mayvid22/Solinas-Product-Design-Challenge/Solinas CAD/Mount/stand assembly/top motor/Component8.step

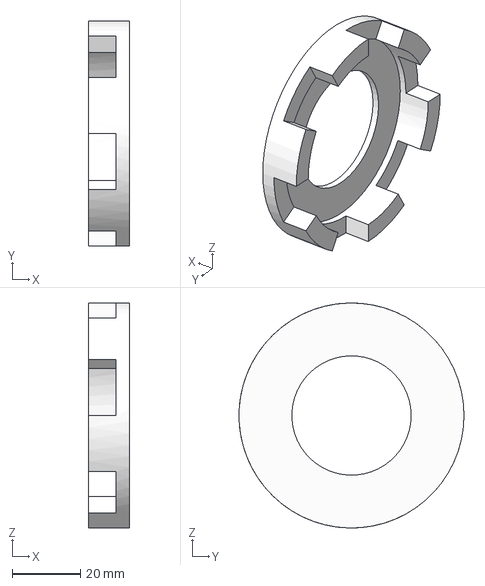
[picture p5: CAD file, 2024-07-06]
Solinas CAD/Mount/stand assembly/top motor/Component8.step
12.0 x 66.0 x 66.0 mm
