mayvid22/Solinas-Product-Design-Challenge/Solinas CAD/Mount/stand support/Part6.step

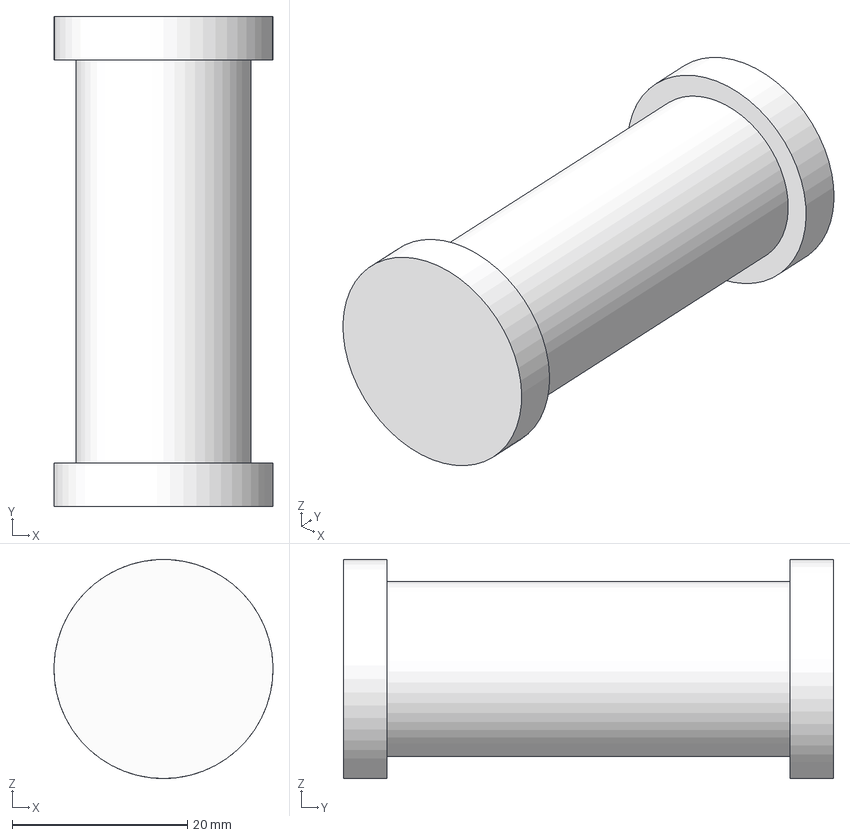
[picture p15: CAD file, 2024-07-06]
Solinas CAD/Mount/stand support/Part6.step
25.0 x 56.0 x 25.0 mm
