mayvid22/Solinas-Product-Design-Challenge/Solinas CAD/Mount/upper part/Component1.step

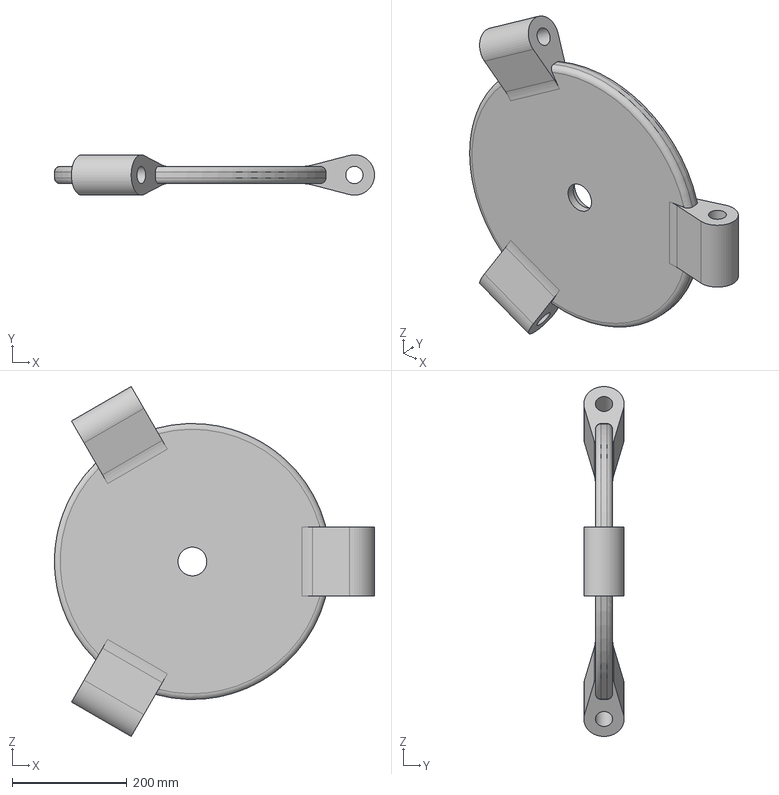
[picture p16: CAD file, 2024-07-06]
Solinas CAD/Mount/upper part/Component1.step
556.9 x 70.3 x 608.9 mm
