mayvid22/Solinas-Product-Design-Challenge/Solinas CAD/Mount/wheel stand/Component3.step

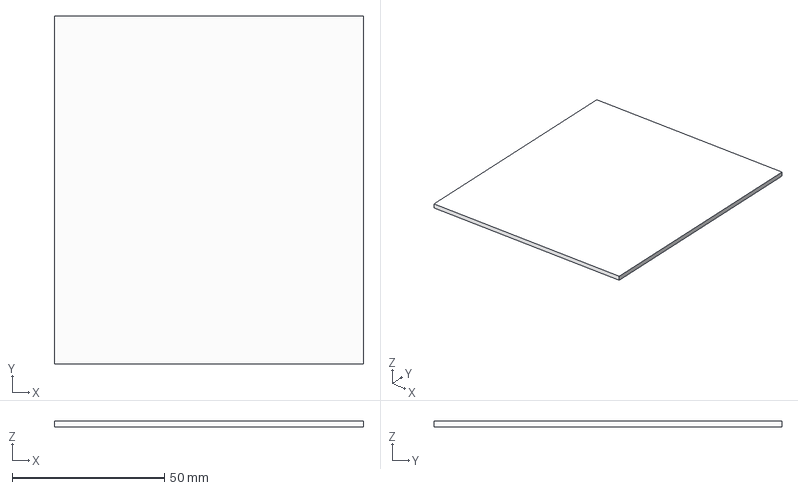
[picture p17: CAD file, 2024-07-06]
Solinas CAD/Mount/wheel stand/Component3.step
101.6 x 114.3 x 2.00 mm
