mayvid22/Solinas-Product-Design-Challenge/Solinas CAD/Shaft/1st cylinder/Component1.step

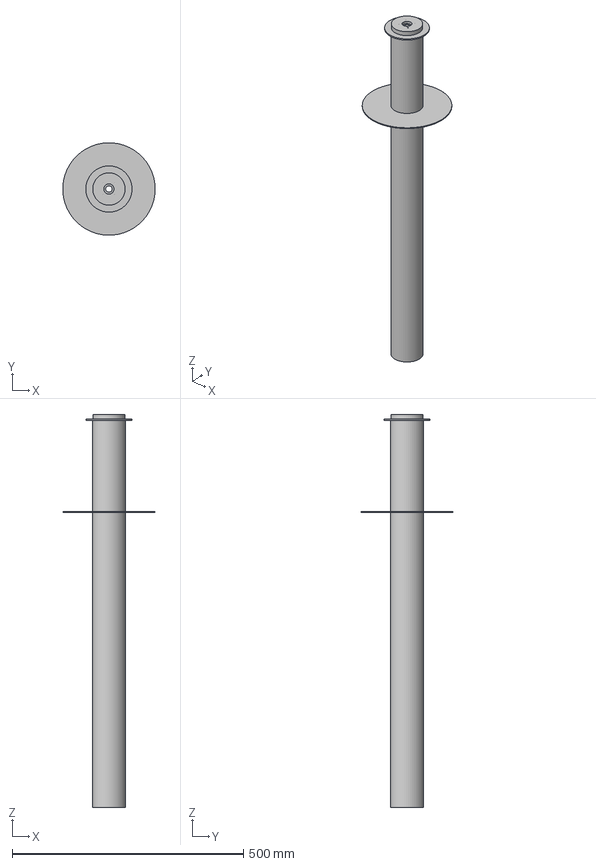
[picture p18: CAD file, 2024-07-06]
Solinas CAD/Shaft/1st cylinder/Component1.step
199.8 x 199.9 x 850.0 mm
