mayvid22/Solinas-Product-Design-Challenge/Solinas CAD/Shaft/1st cylinder/coupler/coupler v1.step

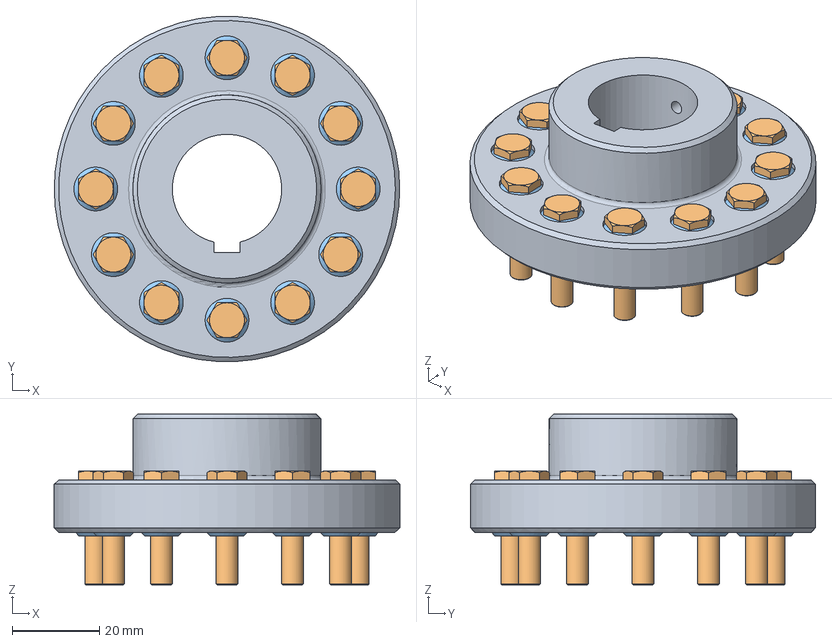
[picture p19: CAD file, 2024-07-06]
Solinas CAD/Shaft/1st cylinder/coupler/coupler v1.step
79.0 x 78.9 x 39.0 mm
c1
csavarr x 12
gumi anya x 48
