mayvid22/Solinas-Product-Design-Challenge/Solinas CAD/Shaft/2nd cylinder/2nd wear ring v4.step

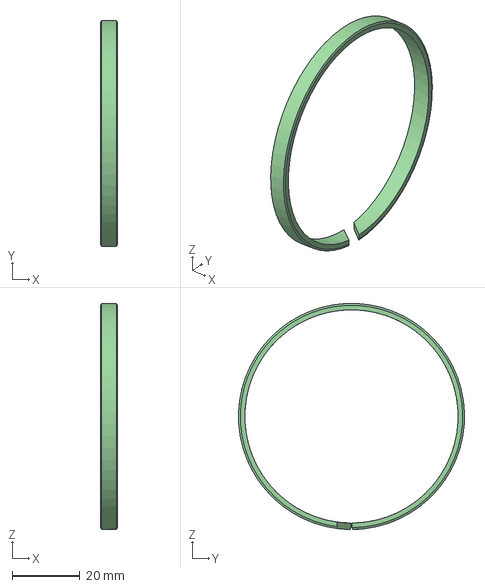
[picture p20: CAD file, 2024-07-06]
Solinas CAD/Shaft/2nd cylinder/2nd wear ring v4.step
5.00 x 67.0 x 67.0 mm
