mayvid22/Solinas-Product-Design-Challenge/Solinas CAD/Shaft/3rd cylinder/3rd wear ring v3.step

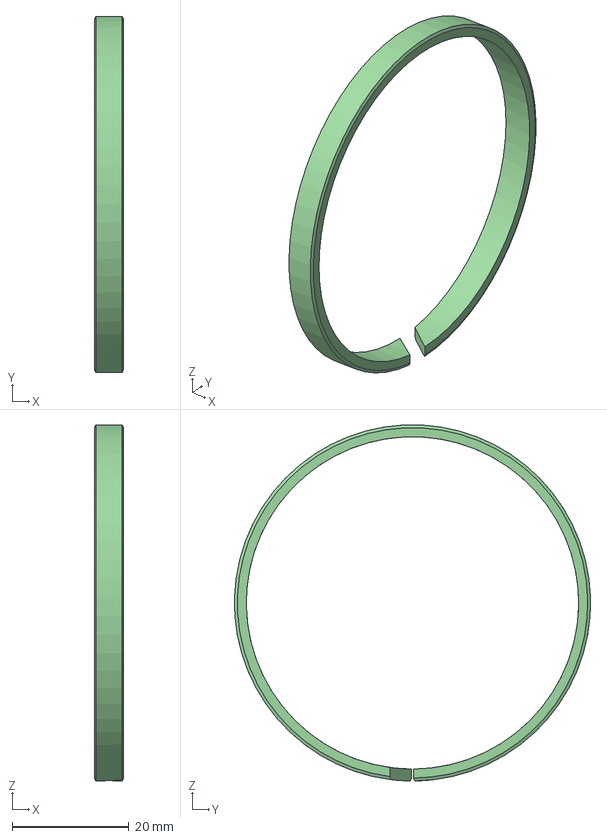
[picture p21: CAD file, 2024-07-06]
Solinas CAD/Shaft/3rd cylinder/3rd wear ring v3.step
5.00 x 61.0 x 61.0 mm
