mayvid22/Solinas-Product-Design-Challenge/Solinas CAD/Shaft/4th cylinder/4th wiper seal v3.step

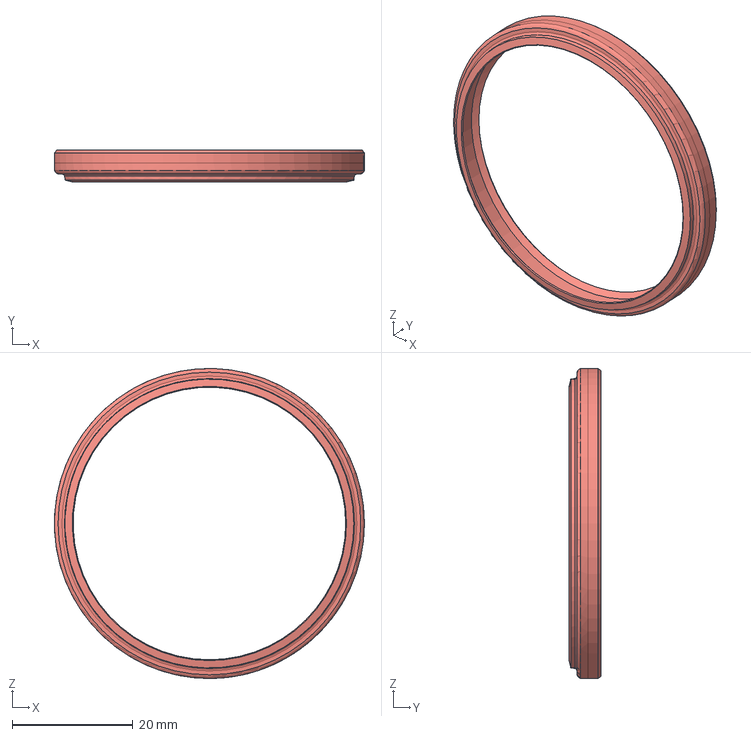
[picture p22: CAD file, 2024-07-06]
Solinas CAD/Shaft/4th cylinder/4th wiper seal v3.step
51.4 x 5.29 x 51.4 mm
