mayvid22/Solinas-Product-Design-Challenge/Solinas CAD/Shaft/5th cylinder/5th wiper seal v2.step

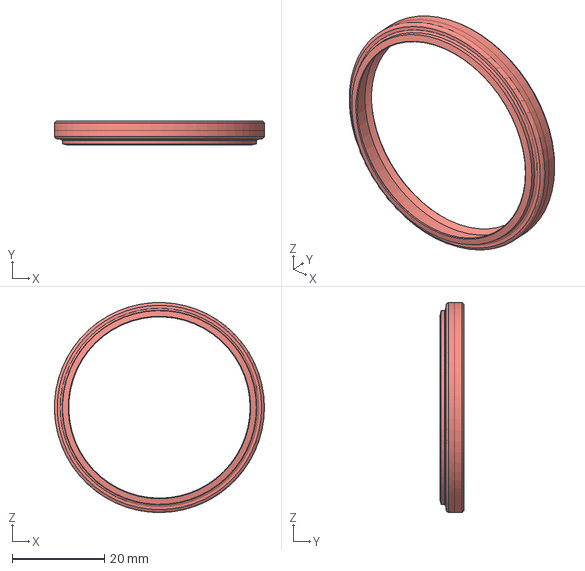
[picture p23: CAD file, 2024-07-06]
Solinas CAD/Shaft/5th cylinder/5th wiper seal v2.step
45.4 x 5.29 x 45.4 mm
