mayvid22/Solinas-Product-Design-Challenge/Solinas CAD/Shaft/6th cylinder/6th wiper seal v4.step

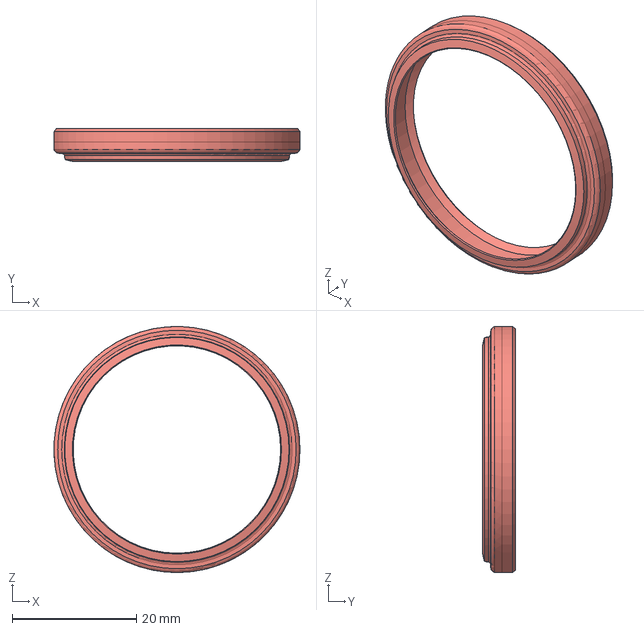
[picture p24: CAD file, 2024-07-06]
Solinas CAD/Shaft/6th cylinder/6th wiper seal v4.step
39.6 x 5.29 x 39.6 mm
