mayvid22/Solinas-Product-Design-Challenge/Solinas CAD/Mount/outer part/Component3.step

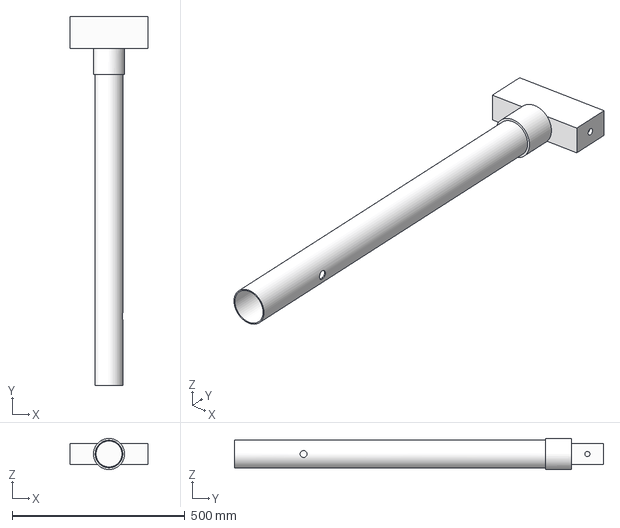
[picture p25: CAD file, 2024-07-06]
Solinas CAD/Mount/outer part/Component3.step
225.0 x 1068.0 x 90.0 mm
