mayvid22/Solinas-Product-Design-Challenge/Solinas CAD/Mount/ratchet_hinge_mirror1.step

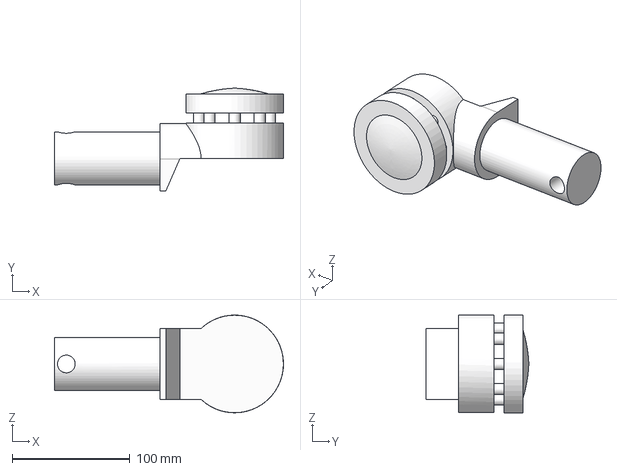
[picture p26: CAD file, 2024-07-06]
Solinas CAD/Mount/ratchet_hinge_mirror1.step
194.4 x 87.2 x 82.9 mm
