mayvid22/Solinas-Product-Design-Challenge/Solinas CAD/Mount/stand assembly/top motor/_MS-SP.step

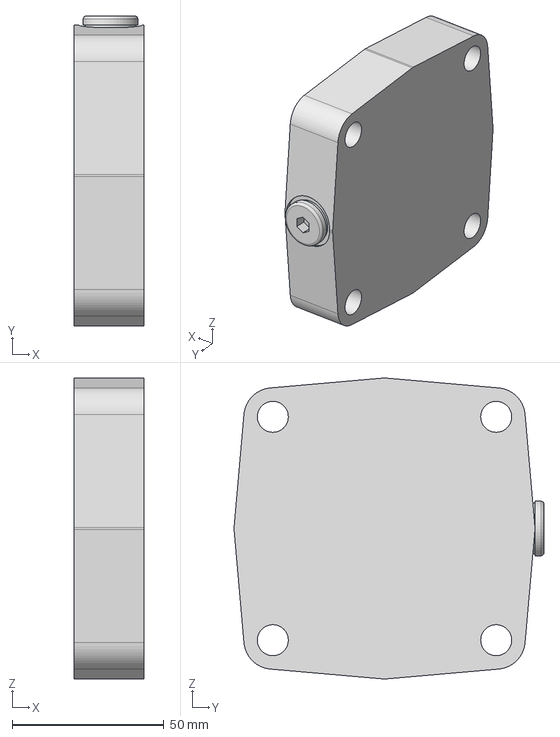
[picture p27: CAD file, 2024-07-06]
Solinas CAD/Mount/stand assembly/top motor/_MS-SP.step
23.0 x 102.0 x 99.1 mm
