mayvid22/Solinas-Product-Design-Challenge/Solinas CAD/Mount/upper part/upper part v7.step

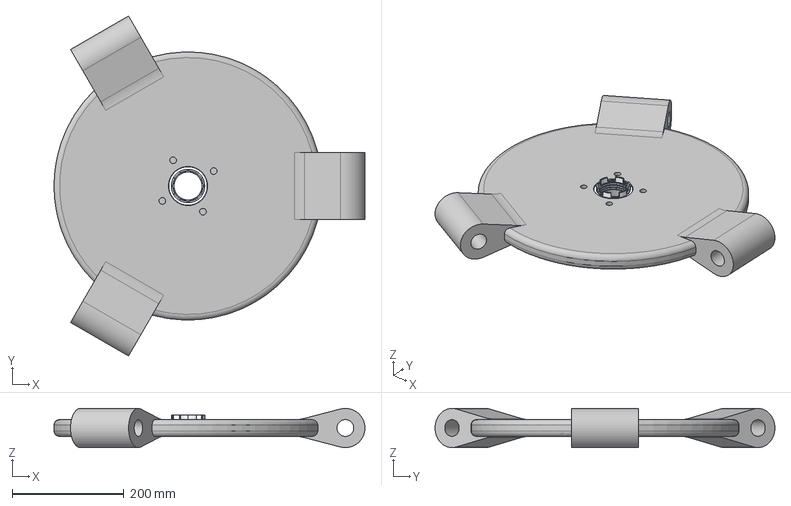
[picture p28: CAD file, 2024-07-06]
Solinas CAD/Mount/upper part/upper part v7.step
556.9 x 608.9 x 70.3 mm
4300N19_Cylindrical-Roller Thrust Bearing
