mayvid22/Solinas-Product-Design-Challenge/Solinas CAD/Mount/wheel stand/castor wheel.step

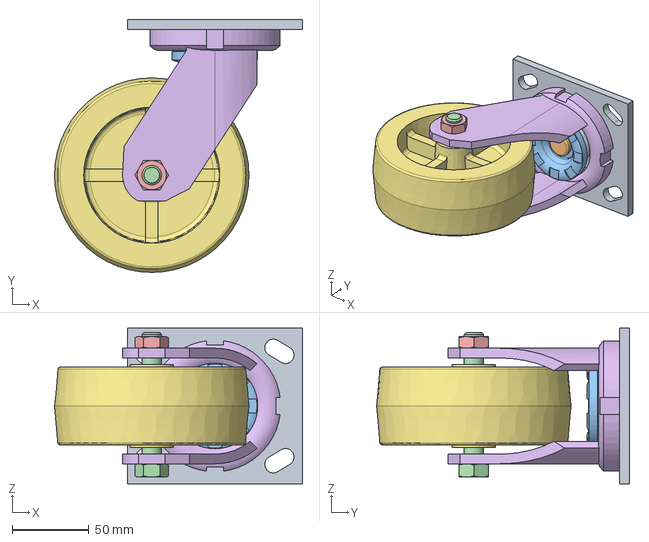
[picture p29: CAD file, 2024-07-06]
Solinas CAD/Mount/wheel stand/castor wheel.step
161.9 x 165.1 x 101.6 mm
