mayvid22/Solinas-Product-Design-Challenge/Solinas CAD/Shaft/1st cylinder/coupler/c1.step

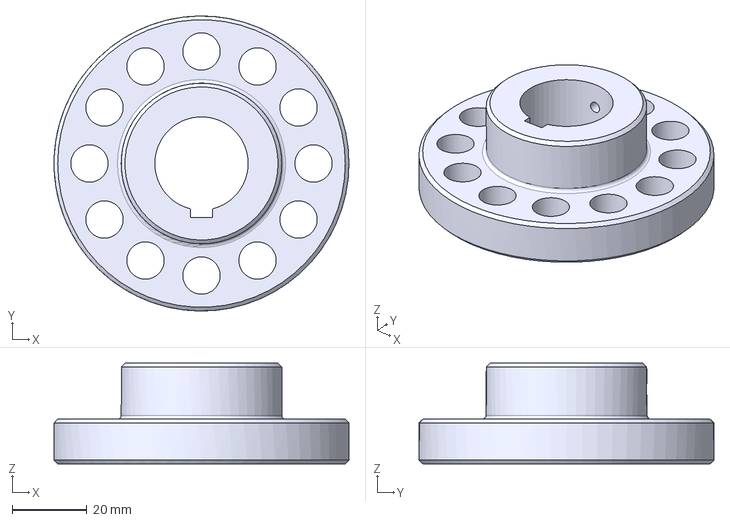
[picture p30: CAD file, 2024-07-06]
Solinas CAD/Shaft/1st cylinder/coupler/c1.step
79.0 x 79.0 x 27.0 mm
