mayvid22/Solinas-Product-Design-Challenge/Solinas CAD/Shaft/2nd cylinder/Component1.step

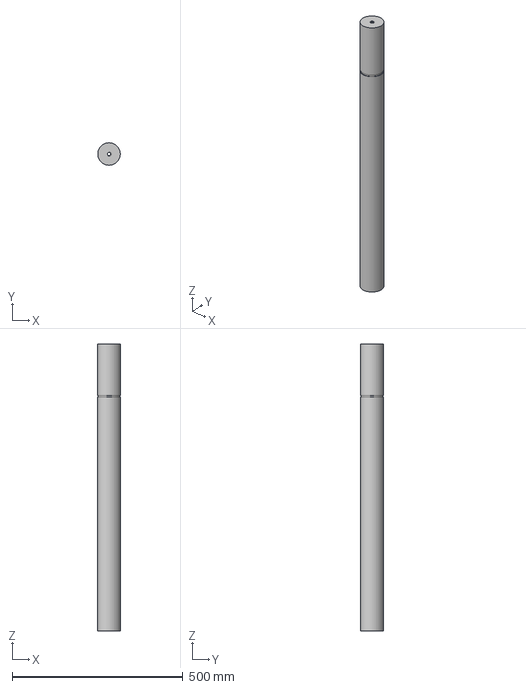
[picture p31: CAD file, 2024-07-06]
Solinas CAD/Shaft/2nd cylinder/Component1.step
65.9 x 66.0 x 840.0 mm
