mayvid22/Solinas-Product-Design-Challenge/Solinas CAD/Shaft/3rd cylinder/Component1.step

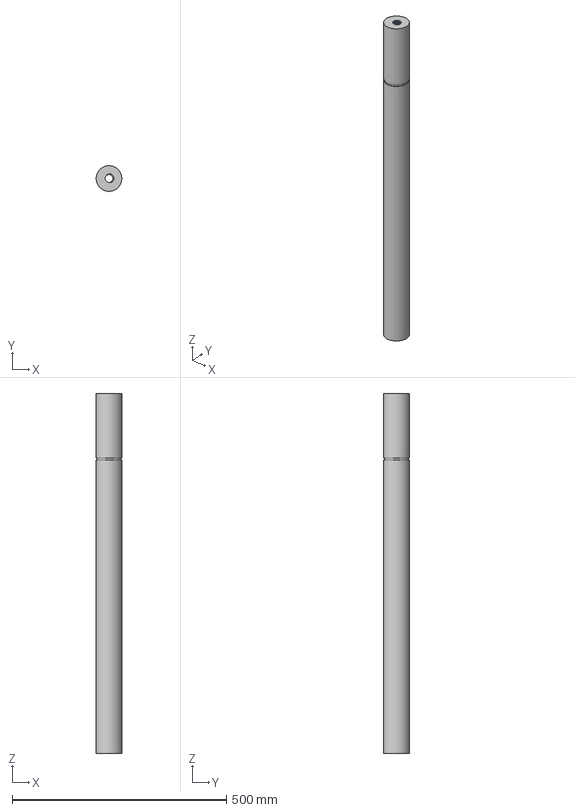
[picture p32: CAD file, 2024-07-06]
Solinas CAD/Shaft/3rd cylinder/Component1.step
59.9 x 60.0 x 840.0 mm
