mayvid22/Solinas-Product-Design-Challenge/Solinas CAD/Shaft/4th cylinder/4th wear ring v4.step

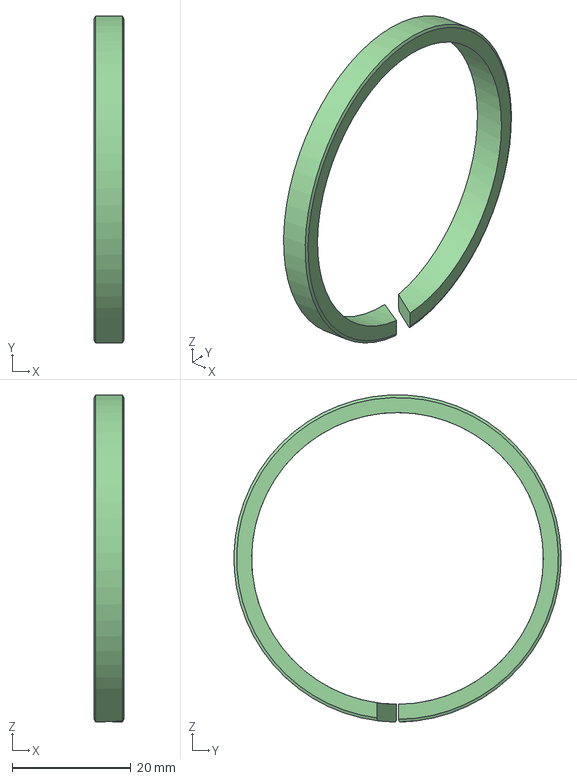
[picture p33: CAD file, 2024-07-06]
Solinas CAD/Shaft/4th cylinder/4th wear ring v4.step
5.00 x 55.0 x 55.0 mm
