mayvid22/Solinas-Product-Design-Challenge/Solinas CAD/Shaft/5th cylinder/5th wear ring v3.step

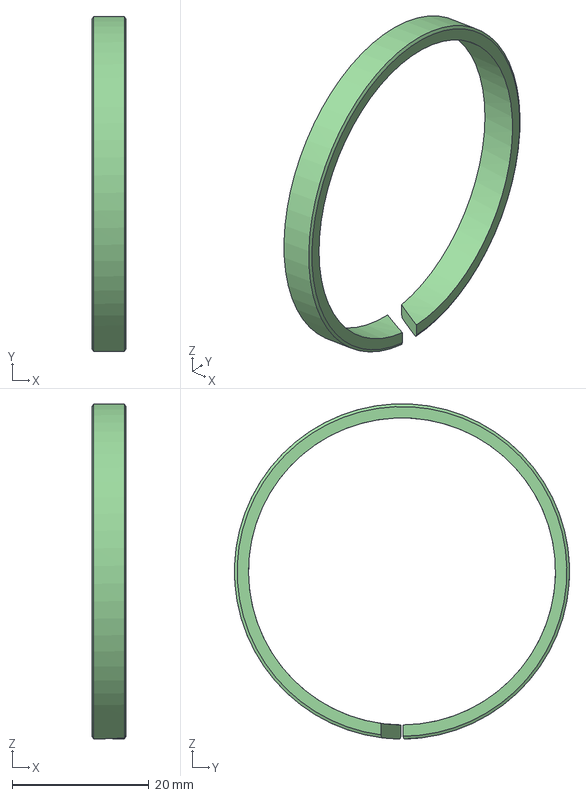
[picture p34: CAD file, 2024-07-06]
Solinas CAD/Shaft/5th cylinder/5th wear ring v3.step
5.00 x 49.0 x 49.0 mm
