mayvid22/Solinas-Product-Design-Challenge/Solinas CAD/Mount/ratchet_hinge_mirror2.step

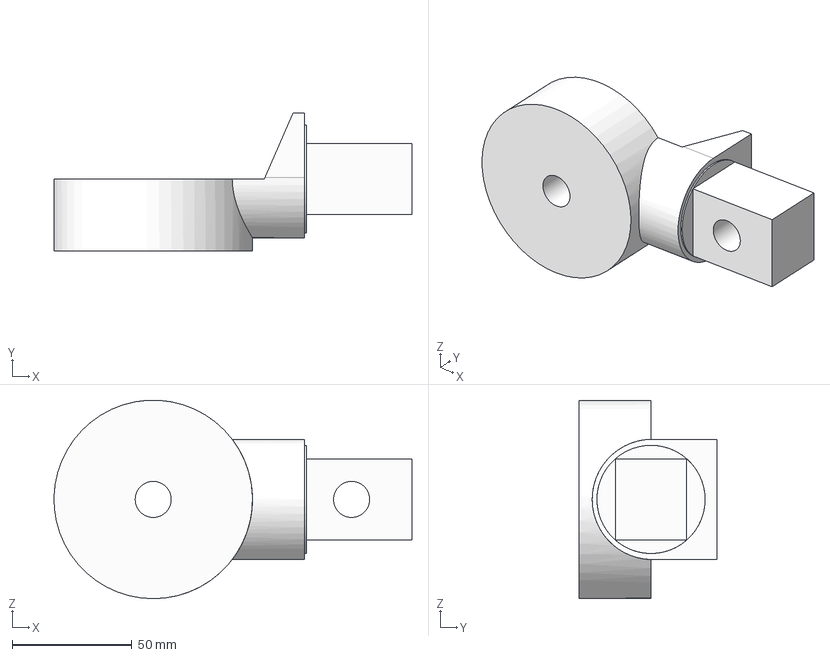
[picture p35: CAD file, 2024-07-06]
Solinas CAD/Mount/ratchet_hinge_mirror2.step
149.3 x 57.8 x 82.7 mm
