mayvid22/Solinas-Product-Design-Challenge/Solinas CAD/Mount/stand assembly/stand support/Part7.step

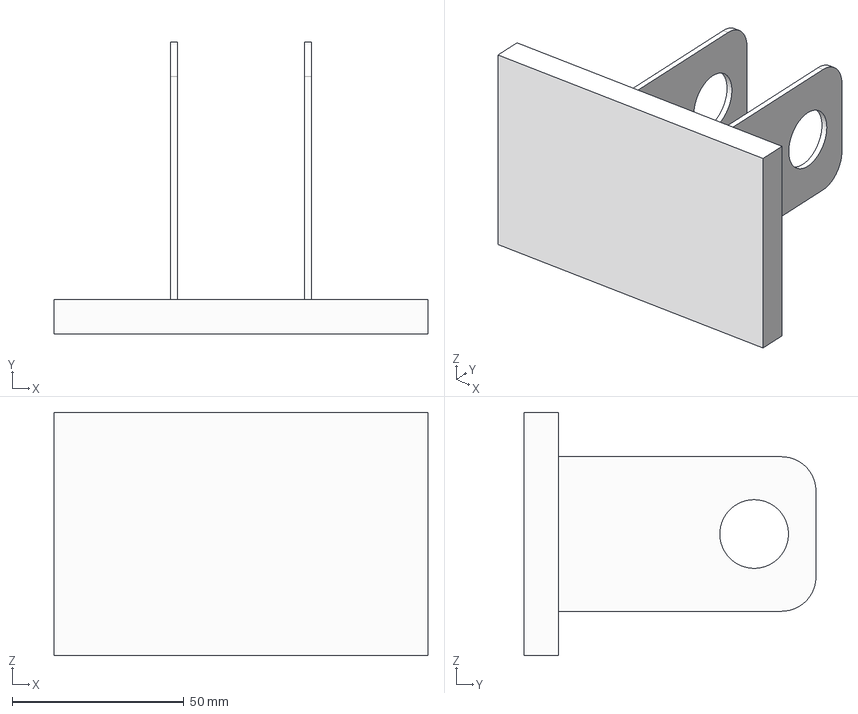
[picture p36: CAD file, 2024-07-06]
Solinas CAD/Mount/stand assembly/stand support/Part7.step
108.9 x 85.0 x 70.9 mm
