mayvid22/Solinas-Product-Design-Challenge/Solinas CAD/Mount/stand assembly/top motor/_MSSH.step

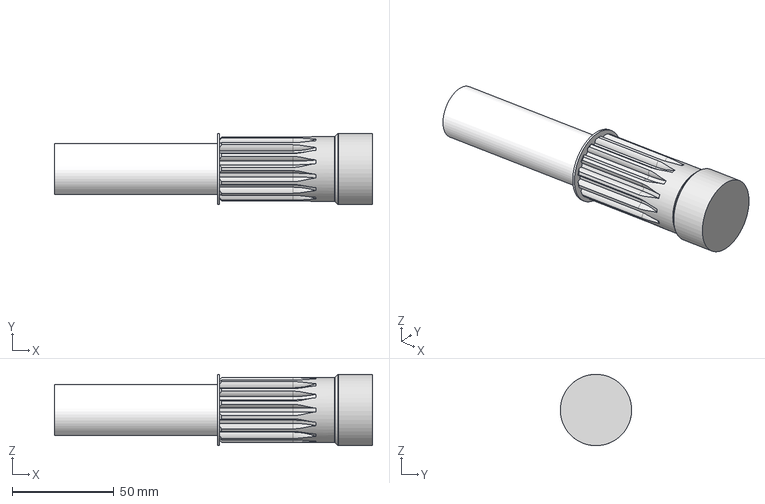
[picture p37: CAD file, 2024-07-06]
Solinas CAD/Mount/stand assembly/top motor/_MSSH.step
156.0 x 35.0 x 35.0 mm
