mayvid22/Solinas-Product-Design-Challenge/Solinas CAD/Mount/stand assembly/wheel stand/wheel stand v3.step

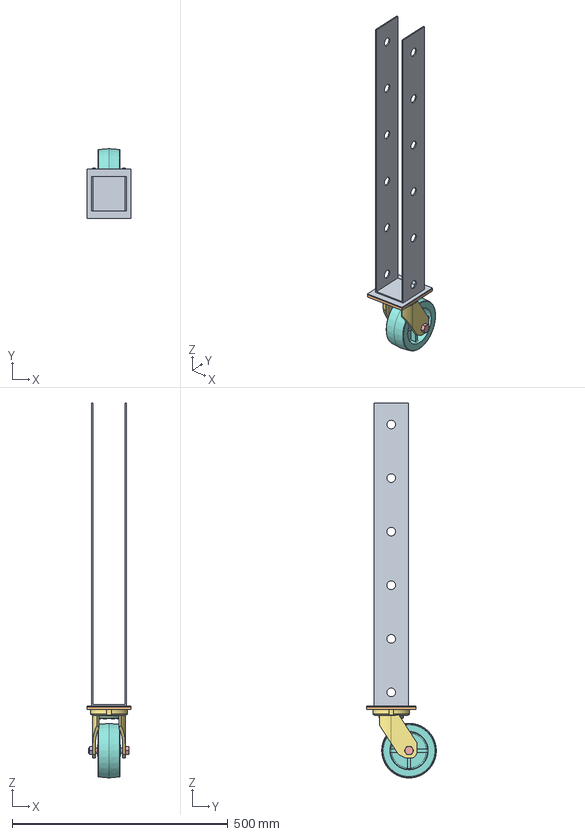
[picture p38: CAD file, 2024-07-06]
Solinas CAD/Mount/stand assembly/wheel stand/wheel stand v3.step
101.6 x 161.9 x 870.1 mm
30305T72_Samson Caster with 4-1-2 x 4 Mounting Plate
