mayvid22/Solinas-Product-Design-Challenge/Solinas CAD/Shaft/1st cylinder/standoff final v1.step

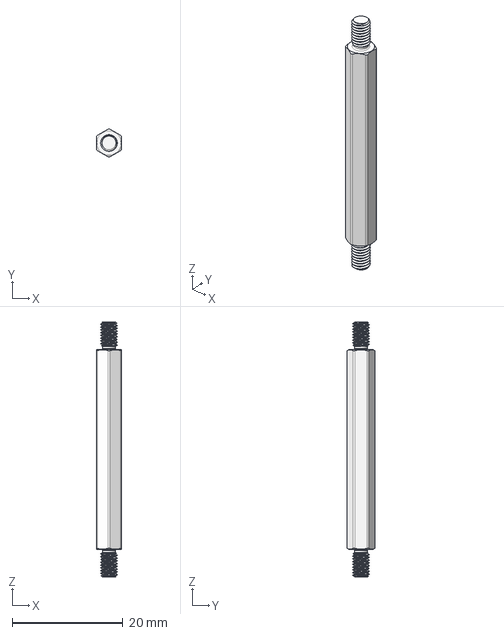
[picture p39: CAD file, 2024-07-06]
Solinas CAD/Shaft/1st cylinder/standoff final v1.step
4.50 x 5.08 x 46.0 mm
