mayvid22/Solinas-Product-Design-Challenge/Solinas CAD/Shaft/2nd cylinder/2nd wiper seal v3.step

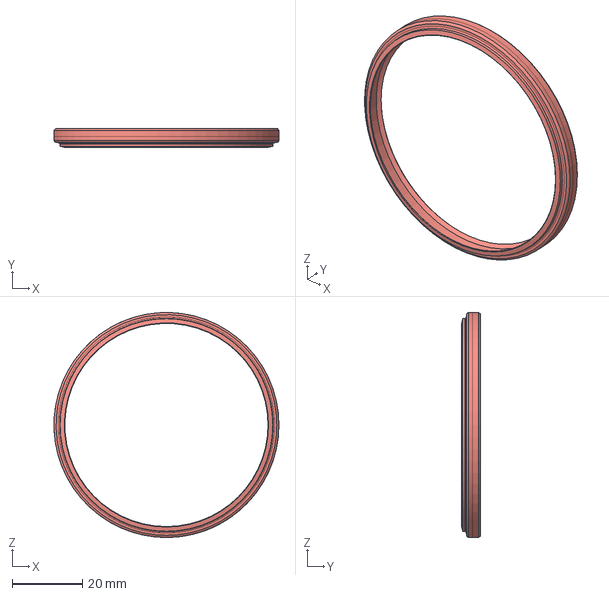
[picture p40: CAD file, 2024-07-06]
Solinas CAD/Shaft/2nd cylinder/2nd wiper seal v3.step
63.9 x 5.29 x 63.9 mm
