mayvid22/Solinas-Product-Design-Challenge/Solinas CAD/Shaft/4th cylinder/Component1.step

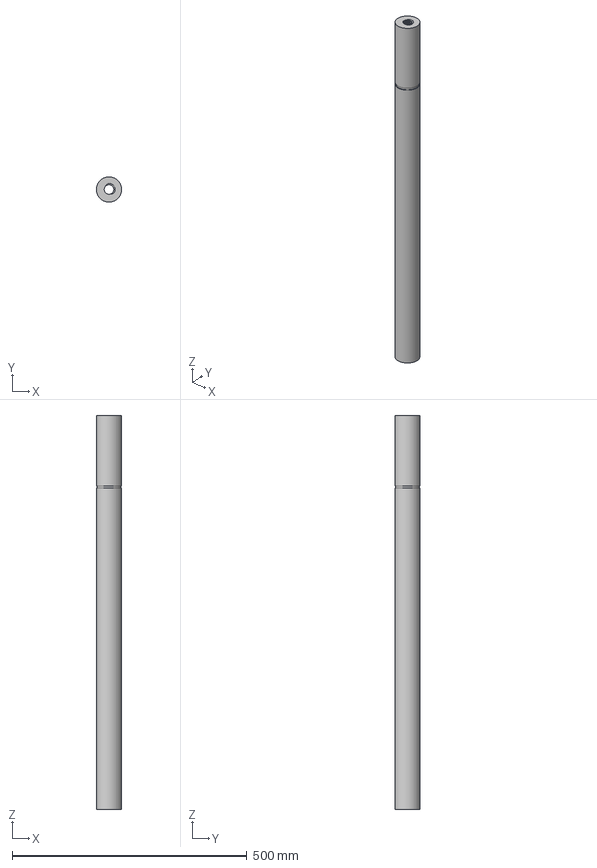
[picture p41: CAD file, 2024-07-06]
Solinas CAD/Shaft/4th cylinder/Component1.step
53.9 x 54.0 x 840.0 mm
