mayvid22/Solinas-Product-Design-Challenge/Solinas CAD/Shaft/5th cylinder/Component1.step

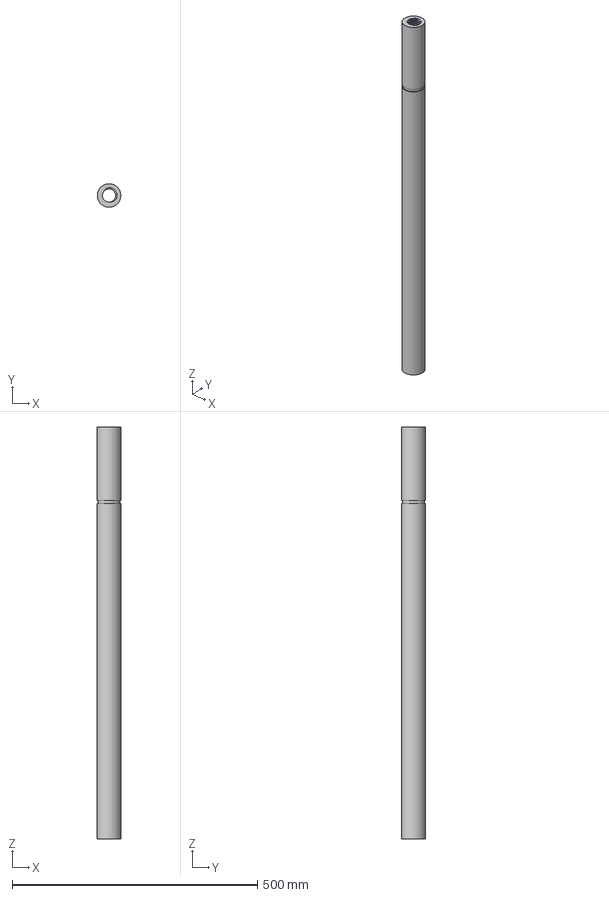
[picture p42: CAD file, 2024-07-06]
Solinas CAD/Shaft/5th cylinder/Component1.step
48.0 x 48.0 x 840.0 mm
