mayvid22/Solinas-Product-Design-Challenge/Solinas CAD/Mount/ratchet_hinge.step

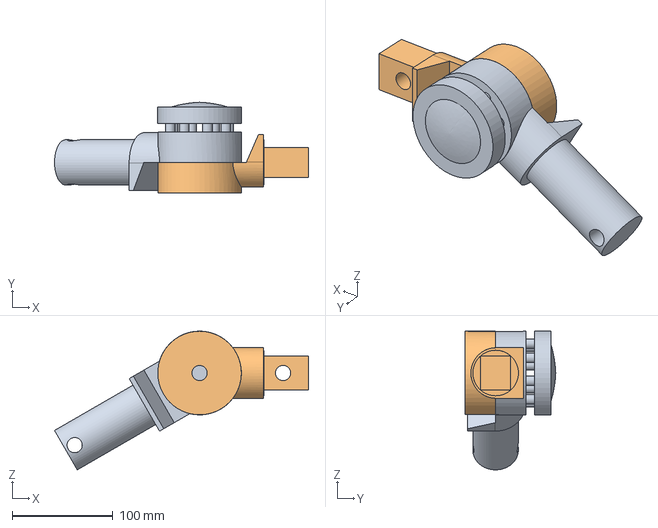
[picture p43: CAD file, 2024-07-06]
Solinas CAD/Mount/ratchet_hinge.step
251.6 x 89.7 x 137.4 mm
