mayvid22/Solinas-Product-Design-Challenge/Solinas CAD/Shaft/1st cylinder/1st wiper seal v5.step

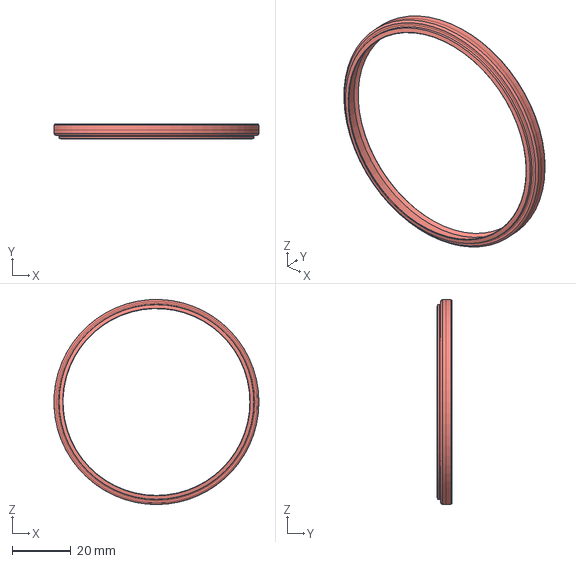
[picture p44: CAD file, 2024-07-06]
Solinas CAD/Shaft/1st cylinder/1st wiper seal v5.step
70.0 x 5.29 x 70.0 mm
