mayvid22/Solinas-Product-Design-Challenge/Solinas CAD/Shaft/6th cylinder/6th wear ring v3.step

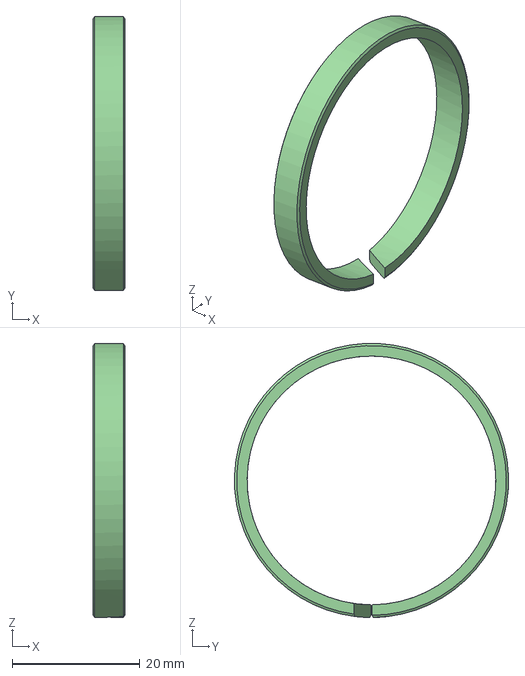
[picture p45: CAD file, 2024-07-06]
Solinas CAD/Shaft/6th cylinder/6th wear ring v3.step
5.00 x 43.0 x 43.0 mm
