mayvid22/Solinas-Product-Design-Challenge/Solinas CAD/Mount/stand assembly/top motor/_MS-VP.step

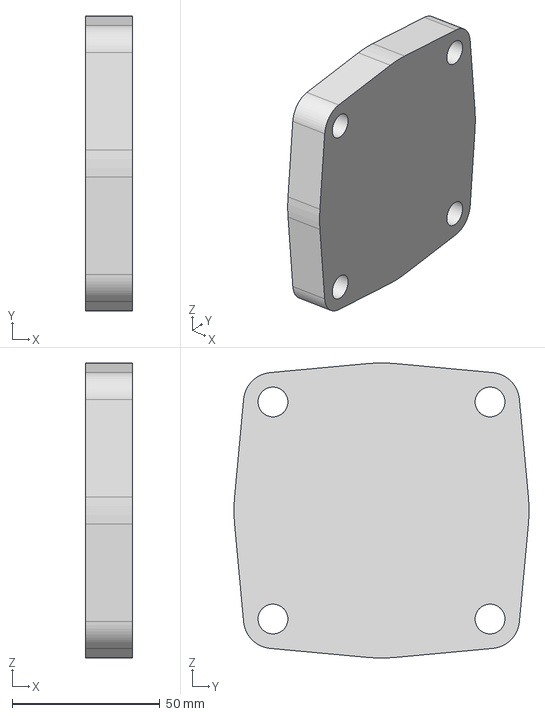
[picture p46: CAD file, 2024-07-06]
Solinas CAD/Mount/stand assembly/top motor/_MS-VP.step
16.0 x 100.0 x 100.0 mm
