mayvid22/Solinas-Product-Design-Challenge/Solinas CAD/Mount/stand assembly/top motor/_MS-P.step

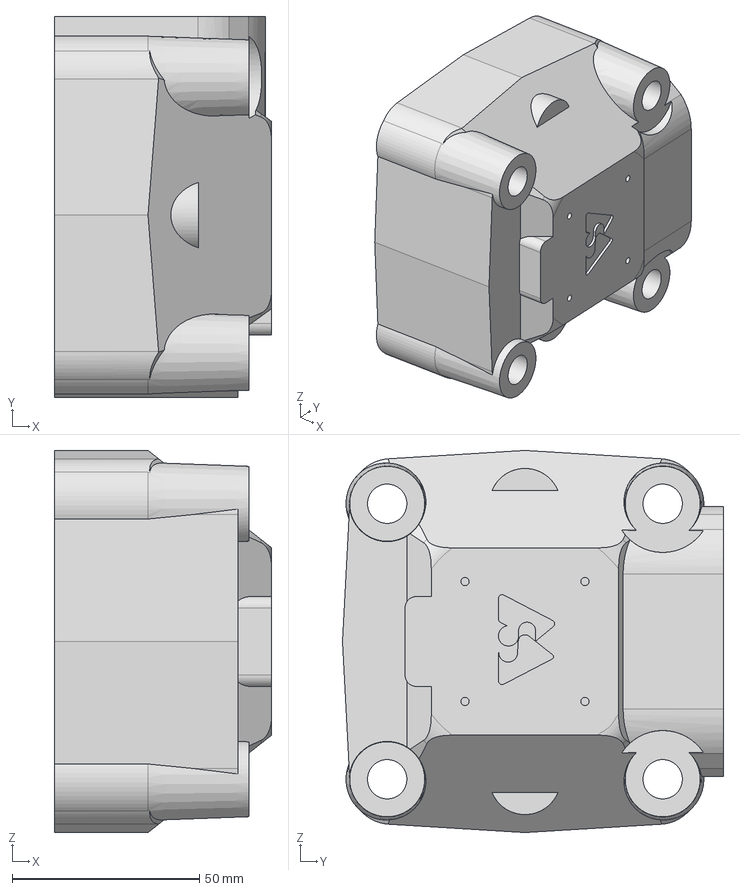
[picture p47: CAD file, 2024-07-06]
Solinas CAD/Mount/stand assembly/top motor/_MS-P.step
58.0 x 101.7 x 102.0 mm
