mayvid22/Solinas-Product-Design-Challenge/Solinas CAD/Shaft/1st cylinder/1st shell v23.step

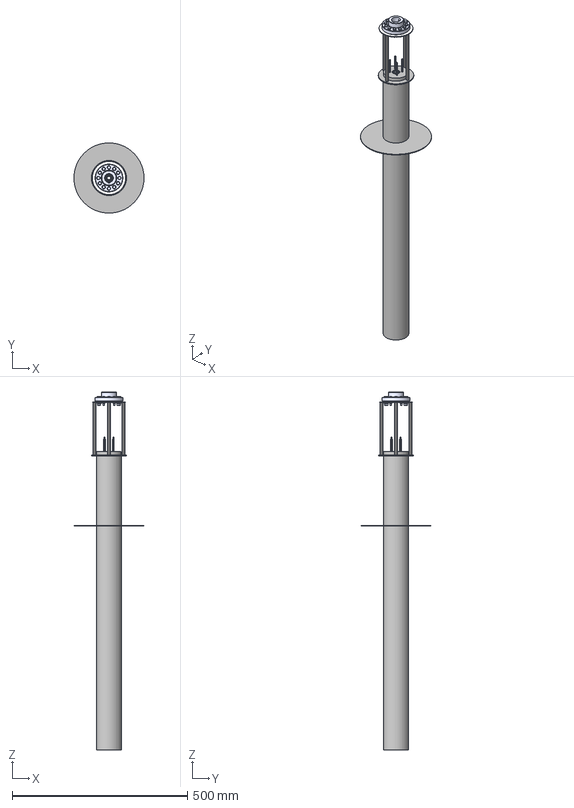
[picture p48: CAD file, 2024-07-06]
Solinas CAD/Shaft/1st cylinder/1st shell v23.step
199.8 x 199.9 x 1020.1 mm
5972K286_Ball Bearing
standoff final x 4
m5 nut x 12
c1
csavarr x 12
gumi anya x 48
