mayvid22/Solinas-Product-Design-Challenge/Solinas CAD/Mount/stand assembly/top motor/_MS315-D.step

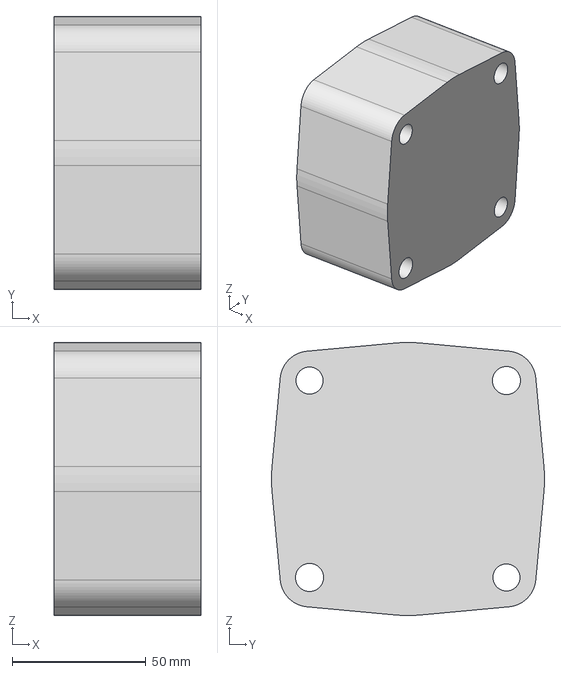
[picture p49: CAD file, 2024-07-06]
Solinas CAD/Mount/stand assembly/top motor/_MS315-D.step
54.8 x 102.0 x 102.0 mm
