mayvid22/Solinas-Product-Design-Challenge/Solinas CAD/Shaft/1st cylinder/Component3.step

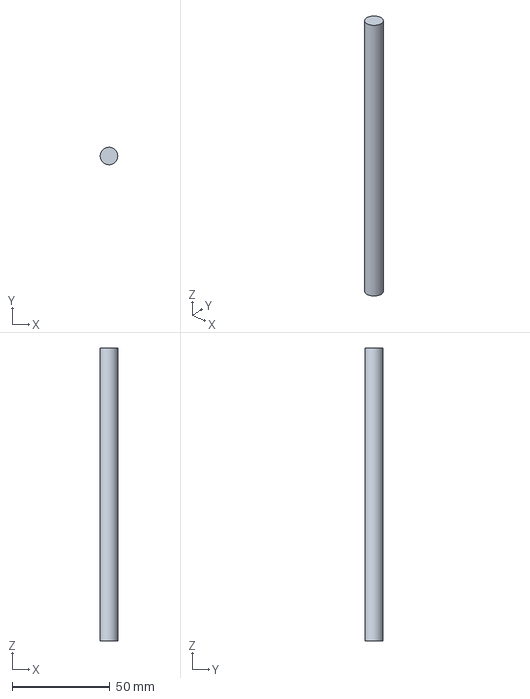
[picture p50: CAD file, 2024-07-06]
Solinas CAD/Shaft/1st cylinder/Component3.step
8.99 x 9.00 x 150.0 mm
