mayvid22/Solinas-Product-Design-Challenge/Solinas CAD/Mount/stand assembly/top motor/top motor v5.step

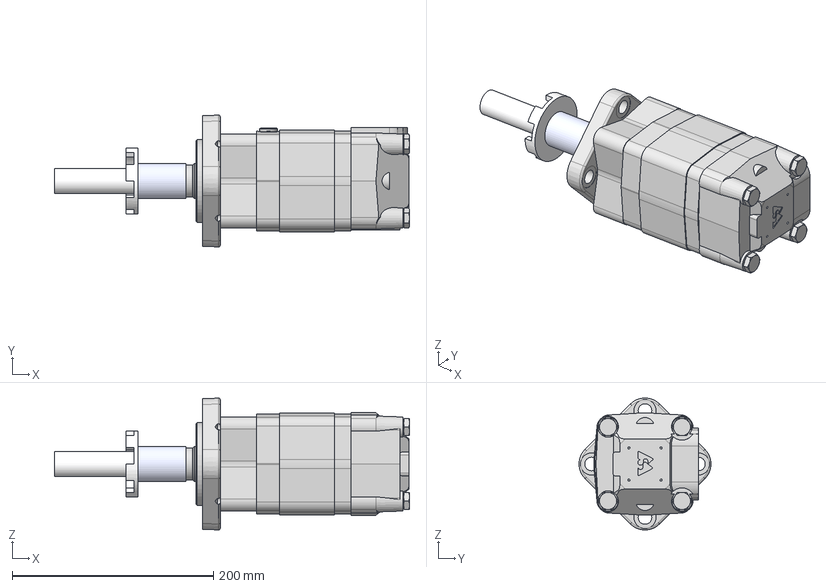
[picture p51: CAD file, 2024-07-06]
Solinas CAD/Mount/stand assembly/top motor/top motor v5.step
353.2 x 131.3 x 131.3 mm
_MS-MF
_MS-SP
_MS315-D
_MS-VP
_MS-P
HI_Hexagon bolt DIN 931-1 M10x1810 x 4
_MSSH
top motor shaft
